vinodkanchi/24-GHz-Movement_Detection__Embedded_System/Embedded_Software_Design/Work050621/First.cydsn/codegentemp/Pin_DACout.h

/*******************************************************************************
* File Name: Pin_DACout.h  
* Version 2.20
*
* Description:
*  This file contains Pin function prototypes and register defines
*
* Note:
*
********************************************************************************
* Copyright 2008-2015, Cypress Semiconductor Corporation.  All rights reserved.
* You may use this file only in accordance with the license, terms, conditions, 
* disclaimers, and limitations in the end user license agreement accompanying 
* the software package with which this file was provided.
*******************************************************************************/

#if !defined(CY_PINS_Pin_DACout_H) /* Pins Pin_DACout_H */
#define CY_PINS_Pin_DACout_H

#include "cytypes.h"
#include "cyfitter.h"
#include "cypins.h"
#include "Pin_DACout_aliases.h"

/* APIs are not generated for P15[7:6] */
#if !(CY_PSOC5A &&\
	 Pin_DACout__PORT == 15 && ((Pin_DACout__MASK & 0xC0) != 0))


/***************************************
*        Function Prototypes             
***************************************/    

/**
* \addtogroup group_general
* @{
*/
void    Pin_DACout_Write(uint8 value);
void    Pin_DACout_SetDriveMode(uint8 mode);
uint8   Pin_DACout_ReadDataReg(void);
uint8   Pin_DACout_Read(void);
void    Pin_DACout_SetInterruptMode(uint16 position, uint16 mode);
uint8   Pin_DACout_ClearInterrupt(void);
/** @} general */

/***************************************
*           API Constants        
***************************************/
/**
* \addtogroup group_constants
* @{
*/
    /** \addtogroup driveMode Drive mode constants
     * \brief Constants to be passed as "mode" parameter in the Pin_DACout_SetDriveMode() function.
     *  @{
     */
        #define Pin_DACout_DM_ALG_HIZ         PIN_DM_ALG_HIZ
        #define Pin_DACout_DM_DIG_HIZ         PIN_DM_DIG_HIZ
        #define Pin_DACout_DM_RES_UP          PIN_DM_RES_UP
        #define Pin_DACout_DM_RES_DWN         PIN_DM_RES_DWN
        #define Pin_DACout_DM_OD_LO           PIN_DM_OD_LO
        #define Pin_DACout_DM_OD_HI           PIN_DM_OD_HI
        #define Pin_DACout_DM_STRONG          PIN_DM_STRONG
        #define Pin_DACout_DM_RES_UPDWN       PIN_DM_RES_UPDWN
    /** @} driveMode */
/** @} group_constants */
    
/* Digital Port Constants */
#define Pin_DACout_MASK               Pin_DACout__MASK
#define Pin_DACout_SHIFT              Pin_DACout__SHIFT
#define Pin_DACout_WIDTH              1u

/* Interrupt constants */
#if defined(Pin_DACout__INTSTAT)
/**
* \addtogroup group_constants
* @{
*/
    /** \addtogroup intrMode Interrupt constants
     * \brief Constants to be passed as "mode" parameter in Pin_DACout_SetInterruptMode() function.
     *  @{
     */
        #define Pin_DACout_INTR_NONE      (uint16)(0x0000u)
        #define Pin_DACout_INTR_RISING    (uint16)(0x0001u)
        #define Pin_DACout_INTR_FALLING   (uint16)(0x0002u)
        #define Pin_DACout_INTR_BOTH      (uint16)(0x0003u) 
    /** @} intrMode */
/** @} group_constants */

    #define Pin_DACout_INTR_MASK      (0x01u) 
#endif /* (Pin_DACout__INTSTAT) */


/***************************************
*             Registers        
***************************************/

/* Main Port Registers */
/* Pin State */
#define Pin_DACout_PS                     (* (reg8 *) Pin_DACout__PS)
/* Data Register */
#define Pin_DACout_DR                     (* (reg8 *) Pin_DACout__DR)
/* Port Number */
#define Pin_DACout_PRT_NUM                (* (reg8 *) Pin_DACout__PRT) 
/* Connect to Analog Globals */                                                  
#define Pin_DACout_AG                     (* (reg8 *) Pin_DACout__AG)                       
/* Analog MUX bux enable */
#define Pin_DACout_AMUX                   (* (reg8 *) Pin_DACout__AMUX) 
/* Bidirectional Enable */                                                        
#define Pin_DACout_BIE                    (* (reg8 *) Pin_DACout__BIE)
/* Bit-mask for Aliased Register Access */
#define Pin_DACout_BIT_MASK               (* (reg8 *) Pin_DACout__BIT_MASK)
/* Bypass Enable */
#define Pin_DACout_BYP                    (* (reg8 *) Pin_DACout__BYP)
/* Port wide control signals */                                                   
#define Pin_DACout_CTL                    (* (reg8 *) Pin_DACout__CTL)
/* Drive Modes */
#define Pin_DACout_DM0                    (* (reg8 *) Pin_DACout__DM0) 
#define Pin_DACout_DM1                    (* (reg8 *) Pin_DACout__DM1)
#define Pin_DACout_DM2                    (* (reg8 *) Pin_DACout__DM2) 
/* Input Buffer Disable Override */
#define Pin_DACout_INP_DIS                (* (reg8 *) Pin_DACout__INP_DIS)
/* LCD Common or Segment Drive */
#define Pin_DACout_LCD_COM_SEG            (* (reg8 *) Pin_DACout__LCD_COM_SEG)
/* Enable Segment LCD */
#define Pin_DACout_LCD_EN                 (* (reg8 *) Pin_DACout__LCD_EN)
/* Slew Rate Control */
#define Pin_DACout_SLW                    (* (reg8 *) Pin_DACout__SLW)

/* DSI Port Registers */
/* Global DSI Select Register */
#define Pin_DACout_PRTDSI__CAPS_SEL       (* (reg8 *) Pin_DACout__PRTDSI__CAPS_SEL) 
/* Double Sync Enable */
#define Pin_DACout_PRTDSI__DBL_SYNC_IN    (* (reg8 *) Pin_DACout__PRTDSI__DBL_SYNC_IN) 
/* Output Enable Select Drive Strength */
#define Pin_DACout_PRTDSI__OE_SEL0        (* (reg8 *) Pin_DACout__PRTDSI__OE_SEL0) 
#define Pin_DACout_PRTDSI__OE_SEL1        (* (reg8 *) Pin_DACout__PRTDSI__OE_SEL1) 
/* Port Pin Output Select Registers */
#define Pin_DACout_PRTDSI__OUT_SEL0       (* (reg8 *) Pin_DACout__PRTDSI__OUT_SEL0) 
#define Pin_DACout_PRTDSI__OUT_SEL1       (* (reg8 *) Pin_DACout__PRTDSI__OUT_SEL1) 
/* Sync Output Enable Registers */
#define Pin_DACout_PRTDSI__SYNC_OUT       (* (reg8 *) Pin_DACout__PRTDSI__SYNC_OUT) 

/* SIO registers */
#if defined(Pin_DACout__SIO_CFG)
    #define Pin_DACout_SIO_HYST_EN        (* (reg8 *) Pin_DACout__SIO_HYST_EN)
    #define Pin_DACout_SIO_REG_HIFREQ     (* (reg8 *) Pin_DACout__SIO_REG_HIFREQ)
    #define Pin_DACout_SIO_CFG            (* (reg8 *) Pin_DACout__SIO_CFG)
    #define Pin_DACout_SIO_DIFF           (* (reg8 *) Pin_DACout__SIO_DIFF)
#endif /* (Pin_DACout__SIO_CFG) */

/* Interrupt Registers */
#if defined(Pin_DACout__INTSTAT)
    #define Pin_DACout_INTSTAT            (* (reg8 *) Pin_DACout__INTSTAT)
    #define Pin_DACout_SNAP               (* (reg8 *) Pin_DACout__SNAP)
    
	#define Pin_DACout_0_INTTYPE_REG 		(* (reg8 *) Pin_DACout__0__INTTYPE)
#endif /* (Pin_DACout__INTSTAT) */

#endif /* CY_PSOC5A... */

#endif /*  CY_PINS_Pin_DACout_H */


/* [] END OF FILE */
