vinodkanchi/24-GHz-Movement_Detection__Embedded_System/Embedded_Software_Design/Work050621/First.cydsn/codegentemp/Pin_PushButton.h

/*******************************************************************************
* File Name: Pin_PushButton.h  
* Version 2.20
*
* Description:
*  This file contains Pin function prototypes and register defines
*
* Note:
*
********************************************************************************
* Copyright 2008-2015, Cypress Semiconductor Corporation.  All rights reserved.
* You may use this file only in accordance with the license, terms, conditions, 
* disclaimers, and limitations in the end user license agreement accompanying 
* the software package with which this file was provided.
*******************************************************************************/

#if !defined(CY_PINS_Pin_PushButton_H) /* Pins Pin_PushButton_H */
#define CY_PINS_Pin_PushButton_H

#include "cytypes.h"
#include "cyfitter.h"
#include "cypins.h"
#include "Pin_PushButton_aliases.h"

/* APIs are not generated for P15[7:6] */
#if !(CY_PSOC5A &&\
	 Pin_PushButton__PORT == 15 && ((Pin_PushButton__MASK & 0xC0) != 0))


/***************************************
*        Function Prototypes             
***************************************/    

/**
* \addtogroup group_general
* @{
*/
void    Pin_PushButton_Write(uint8 value);
void    Pin_PushButton_SetDriveMode(uint8 mode);
uint8   Pin_PushButton_ReadDataReg(void);
uint8   Pin_PushButton_Read(void);
void    Pin_PushButton_SetInterruptMode(uint16 position, uint16 mode);
uint8   Pin_PushButton_ClearInterrupt(void);
/** @} general */

/***************************************
*           API Constants        
***************************************/
/**
* \addtogroup group_constants
* @{
*/
    /** \addtogroup driveMode Drive mode constants
     * \brief Constants to be passed as "mode" parameter in the Pin_PushButton_SetDriveMode() function.
     *  @{
     */
        #define Pin_PushButton_DM_ALG_HIZ         PIN_DM_ALG_HIZ
        #define Pin_PushButton_DM_DIG_HIZ         PIN_DM_DIG_HIZ
        #define Pin_PushButton_DM_RES_UP          PIN_DM_RES_UP
        #define Pin_PushButton_DM_RES_DWN         PIN_DM_RES_DWN
        #define Pin_PushButton_DM_OD_LO           PIN_DM_OD_LO
        #define Pin_PushButton_DM_OD_HI           PIN_DM_OD_HI
        #define Pin_PushButton_DM_STRONG          PIN_DM_STRONG
        #define Pin_PushButton_DM_RES_UPDWN       PIN_DM_RES_UPDWN
    /** @} driveMode */
/** @} group_constants */
    
/* Digital Port Constants */
#define Pin_PushButton_MASK               Pin_PushButton__MASK
#define Pin_PushButton_SHIFT              Pin_PushButton__SHIFT
#define Pin_PushButton_WIDTH              1u

/* Interrupt constants */
#if defined(Pin_PushButton__INTSTAT)
/**
* \addtogroup group_constants
* @{
*/
    /** \addtogroup intrMode Interrupt constants
     * \brief Constants to be passed as "mode" parameter in Pin_PushButton_SetInterruptMode() function.
     *  @{
     */
        #define Pin_PushButton_INTR_NONE      (uint16)(0x0000u)
        #define Pin_PushButton_INTR_RISING    (uint16)(0x0001u)
        #define Pin_PushButton_INTR_FALLING   (uint16)(0x0002u)
        #define Pin_PushButton_INTR_BOTH      (uint16)(0x0003u) 
    /** @} intrMode */
/** @} group_constants */

    #define Pin_PushButton_INTR_MASK      (0x01u) 
#endif /* (Pin_PushButton__INTSTAT) */


/***************************************
*             Registers        
***************************************/

/* Main Port Registers */
/* Pin State */
#define Pin_PushButton_PS                     (* (reg8 *) Pin_PushButton__PS)
/* Data Register */
#define Pin_PushButton_DR                     (* (reg8 *) Pin_PushButton__DR)
/* Port Number */
#define Pin_PushButton_PRT_NUM                (* (reg8 *) Pin_PushButton__PRT) 
/* Connect to Analog Globals */                                                  
#define Pin_PushButton_AG                     (* (reg8 *) Pin_PushButton__AG)                       
/* Analog MUX bux enable */
#define Pin_PushButton_AMUX                   (* (reg8 *) Pin_PushButton__AMUX) 
/* Bidirectional Enable */                                                        
#define Pin_PushButton_BIE                    (* (reg8 *) Pin_PushButton__BIE)
/* Bit-mask for Aliased Register Access */
#define Pin_PushButton_BIT_MASK               (* (reg8 *) Pin_PushButton__BIT_MASK)
/* Bypass Enable */
#define Pin_PushButton_BYP                    (* (reg8 *) Pin_PushButton__BYP)
/* Port wide control signals */                                                   
#define Pin_PushButton_CTL                    (* (reg8 *) Pin_PushButton__CTL)
/* Drive Modes */
#define Pin_PushButton_DM0                    (* (reg8 *) Pin_PushButton__DM0) 
#define Pin_PushButton_DM1                    (* (reg8 *) Pin_PushButton__DM1)
#define Pin_PushButton_DM2                    (* (reg8 *) Pin_PushButton__DM2) 
/* Input Buffer Disable Override */
#define Pin_PushButton_INP_DIS                (* (reg8 *) Pin_PushButton__INP_DIS)
/* LCD Common or Segment Drive */
#define Pin_PushButton_LCD_COM_SEG            (* (reg8 *) Pin_PushButton__LCD_COM_SEG)
/* Enable Segment LCD */
#define Pin_PushButton_LCD_EN                 (* (reg8 *) Pin_PushButton__LCD_EN)
/* Slew Rate Control */
#define Pin_PushButton_SLW                    (* (reg8 *) Pin_PushButton__SLW)

/* DSI Port Registers */
/* Global DSI Select Register */
#define Pin_PushButton_PRTDSI__CAPS_SEL       (* (reg8 *) Pin_PushButton__PRTDSI__CAPS_SEL) 
/* Double Sync Enable */
#define Pin_PushButton_PRTDSI__DBL_SYNC_IN    (* (reg8 *) Pin_PushButton__PRTDSI__DBL_SYNC_IN) 
/* Output Enable Select Drive Strength */
#define Pin_PushButton_PRTDSI__OE_SEL0        (* (reg8 *) Pin_PushButton__PRTDSI__OE_SEL0) 
#define Pin_PushButton_PRTDSI__OE_SEL1        (* (reg8 *) Pin_PushButton__PRTDSI__OE_SEL1) 
/* Port Pin Output Select Registers */
#define Pin_PushButton_PRTDSI__OUT_SEL0       (* (reg8 *) Pin_PushButton__PRTDSI__OUT_SEL0) 
#define Pin_PushButton_PRTDSI__OUT_SEL1       (* (reg8 *) Pin_PushButton__PRTDSI__OUT_SEL1) 
/* Sync Output Enable Registers */
#define Pin_PushButton_PRTDSI__SYNC_OUT       (* (reg8 *) Pin_PushButton__PRTDSI__SYNC_OUT) 

/* SIO registers */
#if defined(Pin_PushButton__SIO_CFG)
    #define Pin_PushButton_SIO_HYST_EN        (* (reg8 *) Pin_PushButton__SIO_HYST_EN)
    #define Pin_PushButton_SIO_REG_HIFREQ     (* (reg8 *) Pin_PushButton__SIO_REG_HIFREQ)
    #define Pin_PushButton_SIO_CFG            (* (reg8 *) Pin_PushButton__SIO_CFG)
    #define Pin_PushButton_SIO_DIFF           (* (reg8 *) Pin_PushButton__SIO_DIFF)
#endif /* (Pin_PushButton__SIO_CFG) */

/* Interrupt Registers */
#if defined(Pin_PushButton__INTSTAT)
    #define Pin_PushButton_INTSTAT            (* (reg8 *) Pin_PushButton__INTSTAT)
    #define Pin_PushButton_SNAP               (* (reg8 *) Pin_PushButton__SNAP)
    
	#define Pin_PushButton_0_INTTYPE_REG 		(* (reg8 *) Pin_PushButton__0__INTTYPE)
#endif /* (Pin_PushButton__INTSTAT) */

#endif /* CY_PSOC5A... */

#endif /*  CY_PINS_Pin_PushButton_H */


/* [] END OF FILE */
