vinodkanchi/24-GHz-Movement_Detection__Embedded_System/Embedded_Software_Design/Work050621/First.cydsn/codegentemp/PinGreen_aliases.h

/*******************************************************************************
* File Name: PinGreen.h  
* Version 2.20
*
* Description:
*  This file contains the Alias definitions for Per-Pin APIs in cypins.h. 
*  Information on using these APIs can be found in the System Reference Guide.
*
* Note:
*
********************************************************************************
* Copyright 2008-2015, Cypress Semiconductor Corporation.  All rights reserved.
* You may use this file only in accordance with the license, terms, conditions, 
* disclaimers, and limitations in the end user license agreement accompanying 
* the software package with which this file was provided.
*******************************************************************************/

#if !defined(CY_PINS_PinGreen_ALIASES_H) /* Pins PinGreen_ALIASES_H */
#define CY_PINS_PinGreen_ALIASES_H

#include "cytypes.h"
#include "cyfitter.h"


/***************************************
*              Constants        
***************************************/
#define PinGreen_0			(PinGreen__0__PC)
#define PinGreen_0_INTR	((uint16)((uint16)0x0001u << PinGreen__0__SHIFT))

#define PinGreen_INTR_ALL	 ((uint16)(PinGreen_0_INTR))

#endif /* End Pins PinGreen_ALIASES_H */


/* [] END OF FILE */
