vinodkanchi/24-GHz-Movement_Detection__Embedded_System/BandPass_Test/Work050621/First.cydsn/codegentemp/WaveDAC8_BuffAmp.h

/*******************************************************************************
* File Name: WaveDAC8_BuffAmp.h  
* Version 1.90
*
* Description:
*  This file contains the function prototypes and constants used in
*  the OpAmp (Analog Buffer) Component.
*
* Note:
*
********************************************************************************
* Copyright 2008-2012, Cypress Semiconductor Corporation.  All rights reserved.
* You may use this file only in accordance with the license, terms, conditions, 
* disclaimers, and limitations in the end user license agreement accompanying 
* the software package with which this file was provided.
*******************************************************************************/


#if !defined(CY_OPAMP_WaveDAC8_BuffAmp_H) 
#define CY_OPAMP_WaveDAC8_BuffAmp_H 

#include "cyfitter.h"
#include "cytypes.h"
#include "CyLib.h"

/* Check to see if required defines such as CY_PSOC5LP are available */
/* They are defined starting with cy_boot v3.0 */
#if !defined (CY_PSOC5LP)
    #error Component OpAmp_v1_90 requires cy_boot v3.0 or later
#endif /* (CY_ PSOC5LP) */


/***************************************
*   Data Struct Definition
***************************************/

/* Low power Mode API Support */
typedef struct
{
    uint8   enableState;
}   WaveDAC8_BuffAmp_BACKUP_STRUCT;

/* Variable describes initial state of the component */
extern uint8 WaveDAC8_BuffAmp_initVar;


/**************************************
*        Function Prototypes 
**************************************/

void WaveDAC8_BuffAmp_Start(void)               ;
void WaveDAC8_BuffAmp_Stop(void)                ;
void WaveDAC8_BuffAmp_SetPower(uint8 power)     ;
void WaveDAC8_BuffAmp_Sleep(void)               ;
void WaveDAC8_BuffAmp_Wakeup(void)              ;
void WaveDAC8_BuffAmp_SaveConfig(void)          ;
void WaveDAC8_BuffAmp_RestoreConfig(void)       ;
void WaveDAC8_BuffAmp_Init(void)                ;
void WaveDAC8_BuffAmp_Enable(void)              ;


/**************************************
*           API Constants
**************************************/

/* Power constants for SetPower() function */
#define WaveDAC8_BuffAmp_LPOCPOWER              (0x00u)
#define WaveDAC8_BuffAmp_LOWPOWER               (0x01u)
#define WaveDAC8_BuffAmp_MEDPOWER               (0x02u)
#define WaveDAC8_BuffAmp_HIGHPOWER              (0x03u)


/**************************************
*           Parameter Defaults        
**************************************/
#define WaveDAC8_BuffAmp_DEFAULT_POWER          (2u)
#define WaveDAC8_BuffAmp_DEFAULT_MODE           (1u)


/**************************************
*             Registers
**************************************/

#define WaveDAC8_BuffAmp_CR_REG                 (* (reg8 *) WaveDAC8_BuffAmp_ABuf__CR)
#define WaveDAC8_BuffAmp_CR_PTR                 (  (reg8 *) WaveDAC8_BuffAmp_ABuf__CR)

#define WaveDAC8_BuffAmp_MX_REG                 (* (reg8 *) WaveDAC8_BuffAmp_ABuf__MX)
#define WaveDAC8_BuffAmp_MX_PTR                 (  (reg8 *) WaveDAC8_BuffAmp_ABuf__MX)

#define WaveDAC8_BuffAmp_SW_REG                 (* (reg8 *) WaveDAC8_BuffAmp_ABuf__SW)
#define WaveDAC8_BuffAmp_SW_PTR                 (  (reg8 *) WaveDAC8_BuffAmp_ABuf__SW)

/* Active mode power manager register */
#define WaveDAC8_BuffAmp_PM_ACT_CFG_REG         (* (reg8 *) WaveDAC8_BuffAmp_ABuf__PM_ACT_CFG)
#define WaveDAC8_BuffAmp_PM_ACT_CFG_PTR         (  (reg8 *) WaveDAC8_BuffAmp_ABuf__PM_ACT_CFG)

/* Alternative mode power manager register */
#define WaveDAC8_BuffAmp_PM_STBY_CFG_REG        (* (reg8 *) WaveDAC8_BuffAmp_ABuf__PM_STBY_CFG)
#define WaveDAC8_BuffAmp_PM_STBY_CFG_PTR        (  (reg8 *) WaveDAC8_BuffAmp_ABuf__PM_STBY_CFG)

/* ANIF.PUMP.CR1 Pump Configuration Register 1 */
#define WaveDAC8_BuffAmp_PUMP_CR1_REG           (* (reg8 *) CYDEV_ANAIF_CFG_PUMP_CR1)
#define WaveDAC8_BuffAmp_PUMP_CR1_PTR           (  (reg8 *) CYDEV_ANAIF_CFG_PUMP_CR1)

/* Trim register defines */
#define WaveDAC8_BuffAmp_TR0_REG                (* (reg8 *) WaveDAC8_BuffAmp_ABuf__TR0)
#define WaveDAC8_BuffAmp_TR0_PTR                (  (reg8 *) WaveDAC8_BuffAmp_ABuf__TR0)

#define WaveDAC8_BuffAmp_TR1_REG                (* (reg8 *) WaveDAC8_BuffAmp_ABuf__TR1)
#define WaveDAC8_BuffAmp_TR1_PTR                (  (reg8 *) WaveDAC8_BuffAmp_ABuf__TR1)


/**************************************
*       Register Constants
**************************************/

/* CX Analog Buffer Input Selection Register */

/* Power mode defines */

/* PM_ACT_CFG (Active Power Mode CFG Register) mask */ 
#define WaveDAC8_BuffAmp_ACT_PWR_EN             WaveDAC8_BuffAmp_ABuf__PM_ACT_MSK 
/* PM_STBY_CFG (Alternative Active Power Mode CFG Register) mask */ 
#define WaveDAC8_BuffAmp_STBY_PWR_EN            WaveDAC8_BuffAmp_ABuf__PM_STBY_MSK 
/* Power mask */
#define WaveDAC8_BuffAmp_PWR_MASK               (0x03u)

/* MX Analog Buffer Input Selection Register */

/* Bit Field  MX_VN */
#define WaveDAC8_BuffAmp_MX_VN_MASK             (0x30u)
#define WaveDAC8_BuffAmp_MX_VN_NC               (0x00u)
#define WaveDAC8_BuffAmp_MX_VN_AG4              (0x10u)
#define WaveDAC8_BuffAmp_MX_VN_AG6              (0x20u)

/* Bit Field  MX_VP */
#define WaveDAC8_BuffAmp_MX_VP_MASK             (0x0Fu)
#define WaveDAC8_BuffAmp_MX_VP_NC               (0x00u)
#define WaveDAC8_BuffAmp_MX_VP_VREF             (0x09u)
#define WaveDAC8_BuffAmp_MX_VP_AG4              (0x01u)
#define WaveDAC8_BuffAmp_MX_VP_AG5              (0x02u)
#define WaveDAC8_BuffAmp_MX_VP_AG6              (0x03u)
#define WaveDAC8_BuffAmp_MX_VP_AG7              (0x04u)
#define WaveDAC8_BuffAmp_MX_VP_ABUS0            (0x05u)
#define WaveDAC8_BuffAmp_MX_VP_ABUS1            (0x06u)
#define WaveDAC8_BuffAmp_MX_VP_ABUS2            (0x07u)
#define WaveDAC8_BuffAmp_MX_VP_ABUS3            (0x08u)

/* SW Analog Buffer Routing Switch Reg */

/* Bit Field  SW */
#define WaveDAC8_BuffAmp_SW_MASK                (0x07u) 
#define WaveDAC8_BuffAmp_SW_SWINP               (0x04u)  /* Enable positive input */
#define WaveDAC8_BuffAmp_SW_SWINN               (0x02u)  /* Enable negative input */

/* Pump configuration register masks */
#define WaveDAC8_BuffAmp_PUMP_CR1_CLKSEL        (0x40u)
#define WaveDAC8_BuffAmp_PUMP_CR1_FORCE         (0x20u)
#define WaveDAC8_BuffAmp_PUMP_CR1_AUTO          (0x10u)

#endif /* CY_OPAMP_WaveDAC8_BuffAmp_H */


/* [] END OF FILE */
