vinodkanchi/24-GHz-Movement_Detection__Embedded_System/BandPass_Test/Work050621/First.cydsn/codegentemp/WaveDAC8_BuffAmp_PM.c

/*******************************************************************************
* File Name: WaveDAC8_BuffAmp_PM.c
* Version 1.90
*
* Description:
*  This file provides the power management source code to the API for the 
*  OpAmp (Analog Buffer) component.
*
* Note:
*
********************************************************************************
* Copyright 2008-2012, Cypress Semiconductor Corporation.  All rights reserved.
* You may use this file only in accordance with the license, terms, conditions, 
* disclaimers, and limitations in the end user license agreement accompanying 
* the software package with which this file was provided.
*******************************************************************************/

#include "WaveDAC8_BuffAmp.h"

static WaveDAC8_BuffAmp_BACKUP_STRUCT  WaveDAC8_BuffAmp_backup;


/*******************************************************************************  
* Function Name: WaveDAC8_BuffAmp_SaveConfig
********************************************************************************
*
* Summary:
*  Saves the current user configuration registers.
* 
* Parameters:
*  void
* 
* Return:
*  void
*
*******************************************************************************/
void WaveDAC8_BuffAmp_SaveConfig(void) 
{
    /* Nothing to save as registers are System reset on retention flops */
}


/*******************************************************************************  
* Function Name: WaveDAC8_BuffAmp_RestoreConfig
********************************************************************************
*
* Summary:
*  Restores the current user configuration registers.
*
* Parameters:
*  void
*
* Return:
*  void
*
*******************************************************************************/
void WaveDAC8_BuffAmp_RestoreConfig(void) 
{
    /* Nothing to restore */
}


/*******************************************************************************   
* Function Name: WaveDAC8_BuffAmp_Sleep
********************************************************************************
*
* Summary:
*  Disables block's operation and saves its configuration. Should be called 
*  just prior to entering sleep.
*
* Parameters:
*  void
*
* Return:
*  void
*
* Global variables:
*  WaveDAC8_BuffAmp_backup: The structure field 'enableState' is modified 
*  depending on the enable state of the block before entering to sleep mode.
*
*******************************************************************************/
void WaveDAC8_BuffAmp_Sleep(void) 
{
    /* Save OpAmp enable state */
    if((WaveDAC8_BuffAmp_PM_ACT_CFG_REG & WaveDAC8_BuffAmp_ACT_PWR_EN) != 0u)
    {
        /* Component is enabled */
        WaveDAC8_BuffAmp_backup.enableState = 1u;
         /* Stops the component */
         WaveDAC8_BuffAmp_Stop();
    }
    else
    {
        /* Component is disabled */
        WaveDAC8_BuffAmp_backup.enableState = 0u;
    }
    /* Saves the configuration */
    WaveDAC8_BuffAmp_SaveConfig();
}


/*******************************************************************************  
* Function Name: WaveDAC8_BuffAmp_Wakeup
********************************************************************************
*
* Summary:
*  Enables block's operation and restores its configuration. Should be called
*  just after awaking from sleep.
*
* Parameters:
*  void
*
* Return:
*  void
*
* Global variables:
*  WaveDAC8_BuffAmp_backup: The structure field 'enableState' is used to 
*  restore the enable state of block after wakeup from sleep mode.
*
*******************************************************************************/
void WaveDAC8_BuffAmp_Wakeup(void) 
{
    /* Restore the user configuration */
    WaveDAC8_BuffAmp_RestoreConfig();

    /* Enables the component operation */
    if(WaveDAC8_BuffAmp_backup.enableState == 1u)
    {
        WaveDAC8_BuffAmp_Enable();
    } /* Do nothing if component was disable before */
}


/* [] END OF FILE */
